TheZeroHz/DiptiBraille/DiptiBraille_V_3_21/ExternalLibrary.h

#ifndef EXTERNALLIBRARY_H
#define EXTERNALLIBRARY_H
#include "features.h"
#include "FS.h"
#include "SD.h"
#include "SPI.h"
#include <Keypad.h>
#include <WiFi.h>
#ifdef HAS_I2S_AMPLIFIER
#include "Audio.h"  //v-1.6.0
#endif
#include "esp_random.h"
#include <Update.h>
#include "AudioTools.h"
#include "BleKeyboard.h"
#include <WiFiManager.h> //v-2.0.7
#endif
