TheZeroHz/DiptiBraille/DiptiBraille_V_3_21/features.h

#ifndef FEATURES_H
#define FEATURES_H
  
/*  
***********************************
******* INCLUDED HARDWARE *********
***********************************
*/

// If any of the hardware is not included then comment to disable....
#define HAS_GSM
#define HAS_I2S_AMPLIFIER
#define HAS_DISPLAY
#define HAS_TFT
#define HAS_VIBRATOR


#endif
